ADPenrose/kintsugi_keeb/acrylic_case/DXF/kintsugi_open_lower.dxf

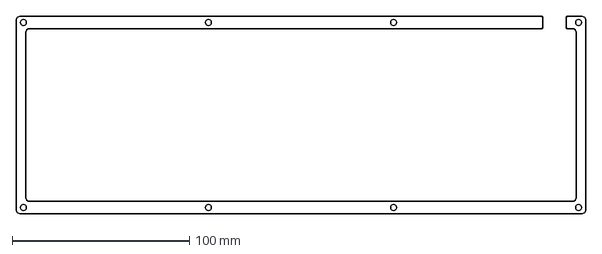
[picture p10: CAD file, 2021-11-19]
acrylic_case/DXF/kintsugi_open_lower.dxf
320.8 x 111.2 mm
